kostya13/doorbell/mel1.asm

	.db 0, 0, B5|en, 2, 0, Dis3|en, 100, 0, B4|en, 150, 0, Gis4|en, 175, 0, G4|en, 200
	.db 0, Dis4|en, 144, 1, C4|en, 148, 1, Dis4, G3|en, 152, 1, C3|en, 88, 2, B3|en, 32
	.db 3, Gis3|en, 36, 3, Gis4|en, 38, 3, C4, F2|en, 132, 3, C3|en, 182, 3, G4|en, 207
	.db 3, F4|en, 232, 3, C4, F3|en, 126, 4, Dis4|en, 176, 4, D4|en, 178, 4, B4|en, 179
	.db 4, F3|en, 181, 4, B3|en, 120, 5, F3|en, 170, 5, D4|en, 220, 5, C4|en, 14, 6
	.db B4|en, 64, 6, B5|en, 66, 6, G2|en, 114, 6, D3|en, 164, 6, G3|en, 214, 6, D4|en
	.db 8, 7, D5|en, 108, 7, B5|en, 208, 7, B5|en, 211, 7, C3|en, 52, 8, G3|en, 149
	.db 8, C4|en, 152, 8, E4|en, 153, 8, G4|en, 155, 8, C5, B4|en, 96, 9, Gis4|en, 100
	.db 9, F3|en, 196, 9, C4|en, 246, 9, Dis4|en, 40, 10, Gis4|en, 140, 10, B5|en, 190, 10
	.db C5|en, 240, 10, C5|en, 242, 10, B3|en, 84, 11, F3|en, 109, 11, Dis4|en, 134, 11, Gis4|en
	.db 159, 11, C5|en, 180, 11, B3|en, 183, 11, B4|en, 184, 11, D4|en, 185, 11, F4|en, 186
	.db 11, B5|en, 128, 12, B5|en, 130, 12, Dis3|en, 228, 12, B4|en, 22, 13, Gis4|en, 47, 13
	.db G4|en, 72, 13, Dis4|en, 74, 13, B4|en, 16, 14, B4|en, 18, 14, Dis4, C3|en, 116, 14
	.db G3|en, 216, 14, B3|en, 60, 15, D4|en, 110, 15, Dis4|en, 160, 15, C4|en, 162, 15, Gis4|en
	.db 166, 15, F2|en, 4, 16, C3|en, 54, 16, G4|en, 79, 16, F4|en, 104, 16, C4|en, 106
	.db 16, F3|en, 204, 16, C4|en, 254, 16, Dis4|en, 48, 17, D4|en, 49, 17, F3|en, 50, 17
	.db B4, B3|en, 248, 17, F3|en, 42, 18, D4|en, 92, 18, C4|en, 142, 18, B4|en, 192, 18
	.db B5|en, 194, 18, G3|en, 242, 18, B4|en, 36, 19, D4|en, 38, 19, D3|en, 86, 19, G4|en
	.db 136, 19, B5|en, 138, 19, G3|en, 30, 20, D5|en, 80, 20, B5|en, 82, 20, C3|en, 180
	.db 20, G3|en, 24, 21, C4|en, 25, 21, E4|en, 26, 21, G4|en, 27, 21, B4|en, 29, 21
	.db C5|en, 224, 21, C4, F3|en, 226, 21, Gis4, Gis3|en, 228, 21, Dis4|en, 168, 22, F3|en, 218
	.db 22, Gis4|en, 12, 23, B5|en, 62, 23, C5|en, 112, 23, F4|en, 115, 23, Gis4, Dis5|en, 117
	.db 23, B3|en, 212, 23, F3|en, 56, 24, F4|en, 59, 24, B5|en, 62, 24, D5, B4|en, 0
	.db 25, Dis4|en, 3, 25, G4|en, 5, 25, B5|en, 7, 25, B4, Dis3|en, 200, 25, Dis3|en, 250
	.db 25, G4|en, 44, 26, Gis4|en, 94, 26, B5|en, 144, 26, C4|en, 145, 26, Dis4|en, 146, 26
	.db B4, C5|en, 88, 27, Gis3|en, 32, 28, B3, D4|en, 34, 28, F3, F4|en, 36, 28, B4|en
	.db 232, 28, B4|en, 26, 29, F4|en, 76, 29, G4|en, 126, 29, Gis4|en, 176, 29, D4|en, 179
	.db 29, G4|en, 181, 29, B5, G3|en, 120, 30, D3|en, 220, 30, G3|en, 64, 31, C3, G3|en
	.db 65, 31, Dis4, C4|en, 8, 32, Dis4|en, 11, 32, B3|en, 58, 32, Dis4|en, 108, 32, F4|en
	.db 158, 32, G4|en, 208, 32, C4|en, 210, 32, Gis4, F4|en, 212, 32, F2|en, 152, 33, C3|en
	.db 202, 33, F3|en, 252, 33, G4|en, 46, 34, F4|en, 96, 34, C4|en, 97, 34, Gis3|en, 98
	.db 34, B3|en, 90, 35, Gis3|en, 140, 35, C4|en, 190, 35, Dis4|en, 240, 35, B3|en, 241, 35
	.db D4, B4|en, 242, 35, F3|en, 184, 36, F3|en, 128, 37, B5, Dis3|en, 228, 37, B4|en, 22
	.db 38, D4|en, 47, 38, G4|en, 72, 38, B5|en, 172, 38, D5|en, 16, 39, E4|en, 20, 39
	.db G4|en, 24, 39, C5, C3|en, 116, 39, G3|en, 216, 39, C4|en, 220, 39, E4|en, 224, 39
	.db G4|en, 226, 39, C5|en, 160, 40, Gis4|en, 162, 40, F2|en, 4, 41, C3|en, 54, 41, C4|en
	.db 79, 41, Dis4|en, 104, 41, Gis4, F3|en, 204, 41, B5|en, 254, 41, C5|en, 48, 42, D4|en
	.db 52, 42, F4|en, 54, 42, B5, B3|en, 148, 42, F3|en, 248, 42, B4|en, 192, 43, D4|en
	.db 196, 43, F4|en, 198, 43, B5, G2|en, 36, 44, D3|en, 136, 44, G3|en, 186, 44, B5|en
	.db 236, 44, C5|en, 30, 45, D5|en, 80, 45, C3|en, 84, 45, G3, E4|en, 86, 45, B4
	.db G4|en, 88, 45, B5|en, 24, 46, C5|en, 224, 46, F2|en, 227, 46, C3, C4|en, 230, 46
	.db F3|en, 233, 46, Dis4, Gis4|en, 12, 48, G4|en, 62, 48, F4|en, 112, 48, B3, C4|en, 114
	.db 48, Gis3, F4|en, 156, 49, D4|en, 0, 50, Gis2, B4|en, 3, 50, Dis4, Gis3|en, 200, 50
	.db Dis3|en, 144, 51, Dis2|en, 150, 51, B3|en, 156, 51, Dis3|en, 162, 51, G3|en, 168, 51, B4|en
	.db 174, 51, Dis4|en, 176, 54, EoS|en
;710
