kostya13/doorbell/river-flows.asm

;River Flows in You, Yiruma
;Copyright © 2013

	.db 0, 0, A6, Fis3|en, 38, 0, Gis5, Cis4|en, 75, 0, A6, Fis4|en, 113, 0, Gis5|en, 150
	.db 0, A6, D3|en, 188, 0, E5, A4|en, 225, 0, A6, E4|en, 7, 1, D5|en, 163, 2
	.db A5|en, 182, 2, Cis5|en, 201, 2, A6, Fis3|en, 238, 2, Gis5, Cis4|en, 20, 3, A6, Fis4|en
	.db 57, 3, Gis5|en, 95, 3, A6, D3|en, 132, 3, E5, A4|en, 170, 3, A6, E4|en, 207
	.db 3, D5|en, 126, 5, A5|en, 154, 5, Cis5|en, 183, 5, A6, Fis3|en, 220, 5, Gis5, Cis4|en
	.db 239, 5, A6|en, 2, 6, Fis4|en, 20, 6, A5|en, 39, 6, Gis5|en, 58, 6, A6|en, 77
	.db 6, D3|en, 95, 6, A5|en, 114, 6, E5, A4|en, 133, 6, A6|en, 152, 6, D4|en, 170
	.db 6, A5|en, 189, 6, D5|en, 208, 6, A5|en, 221, 6, H5|en, 227, 6, Cis5, A3|en, 8
	.db 7, D5, E3|en, 46, 7, E5, A4|en, 83, 7, Cis5|en, 121, 7, H5, E3|en, 158, 7
	.db H4|en, 196, 7, E4|en, 233, 7, A5|en, 252, 7, Gis4|en, 15, 8, A5, Fis3|en, 52, 8
	.db Cis4|en, 90, 8, Fis4|en, 108, 8, E4|en, 127, 8, A5|en, 146, 8, H5|en, 165, 8, Cis5
	.db D3|en, 202, 8, A4|en, 240, 8, D4|en, 21, 9, Cis5|en, 40, 9, D5|en, 59, 9, E5
	.db A3|en, 96, 9, E3|en, 134, 9, A4|en, 171, 9, D5|en, 190, 9, Cis5|en, 209, 9, H5
	.db E3|en, 246, 9, H4|en, 28, 10, E4|en, 84, 10, A5|en, 93, 10, Cis5|en, 103, 10, A6
	.db Fis3|en, 140, 10, Gis5, Cis4|en, 159, 10, A6|en, 178, 10, Fis4|en, 196, 10, A5|en, 215, 10
	.db Gis5|en, 234, 10, A6|en, 253, 10, D3|en, 15, 11, A5|en, 34, 11, E5, A4|en, 53, 11
	.db A6|en, 72, 11, D4|en, 90, 11, A5|en, 109, 11, D5|en, 128, 11, A5|en, 141, 11, H5|en
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
	.db D6|en, 150, 23, E6, A4|en, 168, 23, Cis6|en, 187, 23, H6, E3|en, 206, 23, A6|en, 225
	.db 23, Gis5, E2|en, 6, 24, E5, H3|en, 44, 24, H5, E3|en, 81, 24, Gis4, Gis3|en, 119
	.db 24, E4, H4|en, 0, 25, EoS|en

;Create by programm "ConTiny45" ver 1.2  (www.dubrovenko.ru)
