kostya13/doorbell/mel2.asm

	.db 0, 0, C3|en, 1, 0, E4|en, 2, 0, A5|en, 50, 0, E3|en, 75, 0, H5|en, 100
	.db 0, G3|en, 150, 0, H4, E4|en, 200, 0, G3|en, 250, 0, H4|en, 44, 1, E4|en, 94
	.db 1, H4|en, 144, 1, C3|en, 145, 1, E4|en, 146, 1, A5|en, 194, 1, E3|en, 219, 1
	.db H5|en, 244, 1, G3|en, 38, 2, H4, E4|en, 88, 2, G3|en, 138, 2, H4|en, 188, 2
	.db E4|en, 238, 2, H4|en, 32, 3, H3|en, 33, 3, E4|en, 34, 3, A5|en, 82, 3, D3|en
	.db 107, 3, H5|en, 132, 3, Fis3|en, 182, 3, A4, D5|en, 232, 3, Fis3|en, 26, 4, A4|en
	.db 76, 4, D4|en, 126, 4, A4|en, 176, 4, H3|en, 177, 4, E4|en, 178, 4, A5|en, 226
	.db 4, D3|en, 251, 4, H5|en, 20, 5, Fis3|en, 70, 5, A4, D5|en, 120, 5, Fis3|en, 170
	.db 5, A4|en, 220, 5, D4|en, 14, 6, A4|en, 64, 6, C3|en, 65, 6, E4|en, 66, 6
	.db A5|en, 114, 6, E3|en, 139, 6, H5|en, 164, 6, G3|en, 214, 6, H4, E4|en, 8, 7
	.db G3|en, 58, 7, H4|en, 108, 7, E4|en, 158, 7, H4|en, 208, 7, C3|en, 209, 7, E4|en
	.db 210, 7, A5|en, 2, 8, E3|en, 27, 8, H5|en, 52, 8, G3|en, 102, 8, H4, E4|en
	.db 152, 8, G3|en, 202, 8, H4|en, 252, 8, E4|en, 46, 9, H4|en, 96, 9, H3|en, 97
	.db 9, E4|en, 98, 9, A5|en, 146, 9, D3|en, 171, 9, H5|en, 196, 9, Fis3|en, 246, 9
	.db A4, D5|en, 40, 10, Fis3|en, 90, 10, A4|en, 140, 10, D4|en, 190, 10, A4|en, 240, 10
	.db H3|en, 241, 10, E4|en, 242, 10, A5|en, 34, 11, D3|en, 59, 11, H5|en, 84, 11, Fis3|en
	.db 134, 11, A4, E4|en, 136, 11, E5|en, 184, 11, Fis3|en, 234, 11, D4, D5|en, 28, 12
	.db A4, H5|en, 53, 12, A5|en, 78, 12, E3|en, 128, 12, E3|en, 129, 12, A4|en, 130, 12
	.db G4|en, 178, 12, G3|en, 228, 12, H4|en, 22, 13, D4|en, 72, 13, H4|en, 122, 13, Fis4|en
	.db 172, 13, G3|en, 222, 13, H4, G4|en, 16, 14, Dis3|en, 18, 14, G4|en, 66, 14, G3|en
	.db 116, 14, H4|en, 166, 14, Dis4|en, 216, 14, H4, A5|en, 10, 15, G3|en, 35, 15, G4|en
	.db 60, 15, Dis4|en, 110, 15, H4, A5|en, 160, 15, D3|en, 162, 15, H5|en, 210, 15, Fis3|en
	.db 4, 16, A4|en, 54, 16, D4|en, 104, 16, A4, H5|en, 154, 16, Fis4|en, 179, 16, D5|en
	.db 204, 16, Fis3|en, 254, 16, A4, E5|en, 48, 17, Cis3|en, 50, 17, H5|en, 98, 17, E3|en
	.db 148, 17, G3|en, 198, 17, H4|en, 248, 17, G3|en, 42, 18, H4, A5|en, 92, 18, E4
	.db G4|en, 142, 18, H4, Fis4|en, 192, 18, C3|en, 194, 18, E4|en, 242, 18, E3|en, 36, 19
	.db G3|en, 86, 19, H4|en, 136, 19, G3, H5|en, 186, 19, H4|en, 236, 19, E4, A5|en, 30
	.db 20, H4|en, 80, 20, H3|en, 82, 20, Fis4|en, 130, 20, D3|en, 180, 20, Fis3|en, 230, 20
	.db A4|en, 24, 21, Fis3|en, 74, 21, A4|en, 124, 21, D4|en, 174, 21, A4|en, 224, 21, E3|en
	.db 226, 21, E4|en, 18, 22, D3|en, 68, 22, Fis3|en, 118, 22, A4|en, 120, 22, A5|en, 168
	.db 22, Fis3|en, 218, 22, A4|en, 12, 23, D4, H5|en, 62, 23, A4|en, 112, 23, E2|en, 116
	.db 23, D4|en, 119, 23, E5|en, 124, 23, H3|en, 128, 23, E3|en, 144, 26, EoS|en
;510
